MohamadAminGhanoum/Smart-room-Screen/assets/Screenshot 2026-01-31 at 23.26.51.png

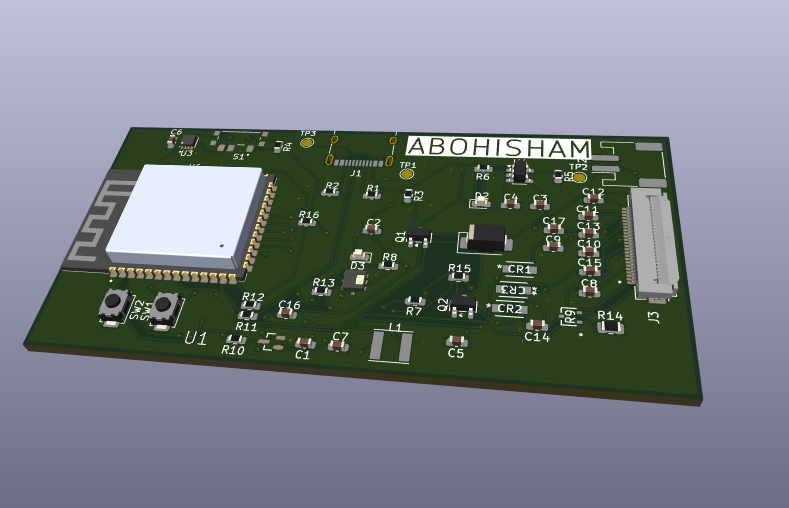
assets/Screenshot 2026-01-31 at 23.26.51.png
