MohamadAminGhanoum/Smart-room-Screen/assets/Screenshot 2026-01-23 at 23.30.38.png

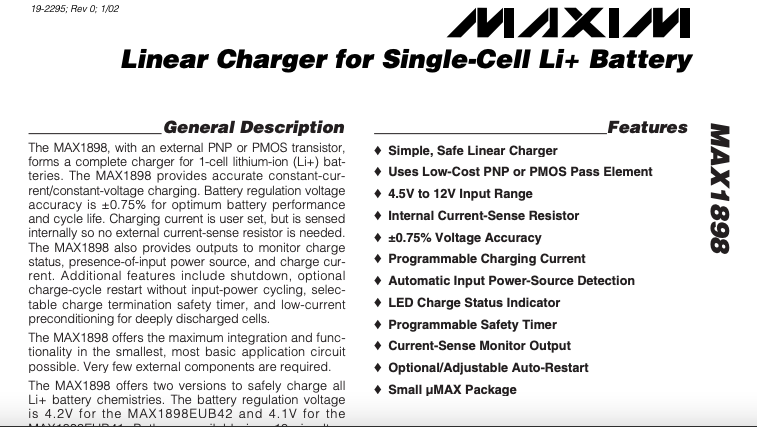
assets/Screenshot 2026-01-23 at 23.30.38.png
