MohamadAminGhanoum/Smart-room-Screen/assets/Screenshot 2026-01-24 at 14.30.04.png

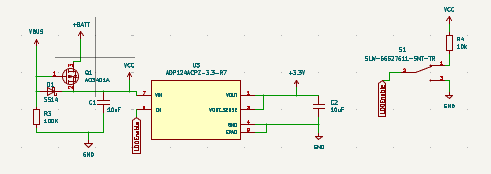
assets/Screenshot 2026-01-24 at 14.30.04.png
