MohamadAminGhanoum/Smart-room-Screen/assets/Screenshot 2026-01-24 at 15.07.33.png

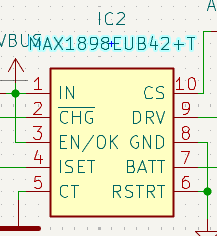
assets/Screenshot 2026-01-24 at 15.07.33.png
