MohamadAminGhanoum/Smart-room-Screen/assets/Screenshot 2026-01-24 at 16.34.39.png

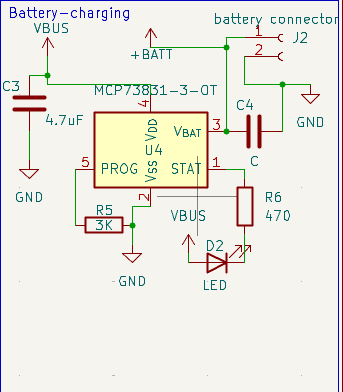
assets/Screenshot 2026-01-24 at 16.34.39.png
