MohamadAminGhanoum/Smart-room-Screen/assets/Screenshot 2026-01-24 at 16.39.06.png

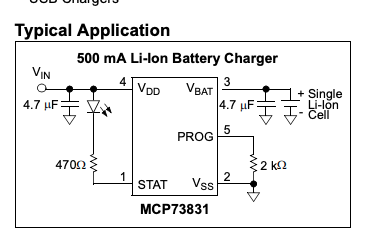
assets/Screenshot 2026-01-24 at 16.39.06.png
