MohamadAminGhanoum/Smart-room-Screen/assets/Screenshot 2026-01-24 at 17.12.46.png

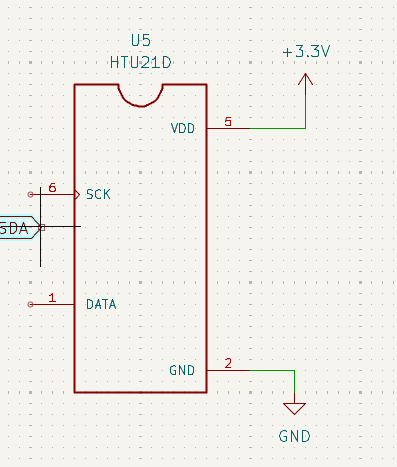
assets/Screenshot 2026-01-24 at 17.12.46.png
