MohamadAminGhanoum/Smart-room-Screen/assets/Screenshot 2026-01-24 at 17.20.51.png

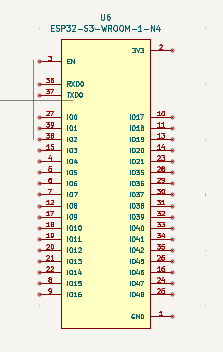
assets/Screenshot 2026-01-24 at 17.20.51.png
