MohamadAminGhanoum/Smart-room-Screen/assets/Screenshot 2026-01-24 at 19.51.00.png

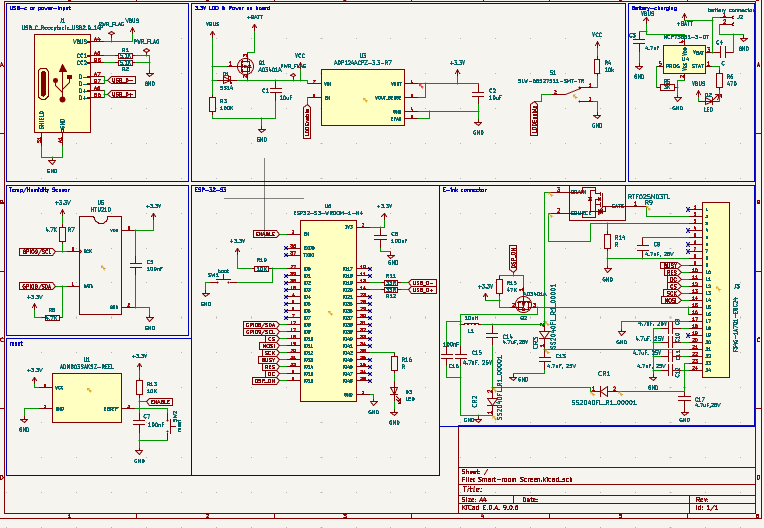
assets/Screenshot 2026-01-24 at 19.51.00.png
