MohamadAminGhanoum/Smart-room-Screen/assets/Screenshot 2026-01-24 at 19.59.05.png

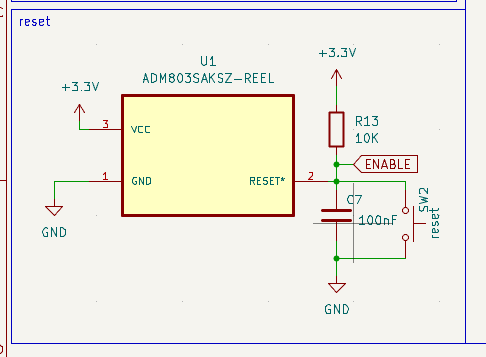
assets/Screenshot 2026-01-24 at 19.59.05.png
