MohamadAminGhanoum/Smart-room-Screen/assets/Screenshot 2026-01-24 at 20.54.59.png

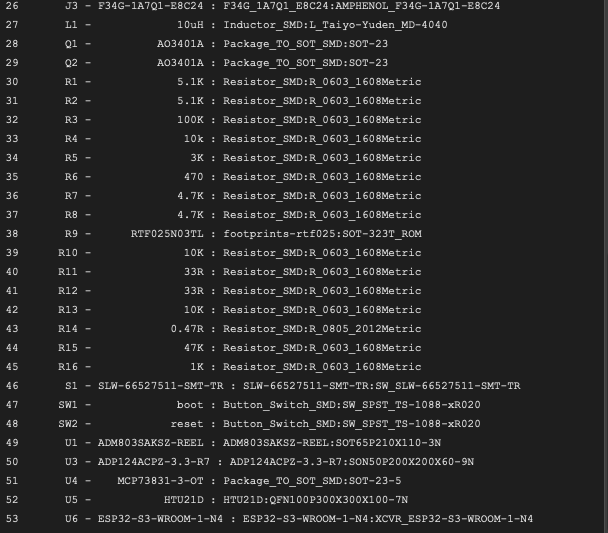
assets/Screenshot 2026-01-24 at 20.54.59.png
