MohamadAminGhanoum/Smart-room-Screen/assets/Screenshot 2026-01-25 at 15.22.35.png

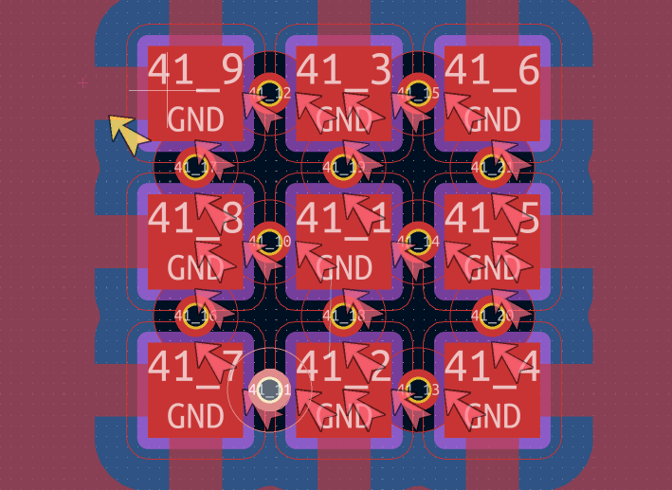
assets/Screenshot 2026-01-25 at 15.22.35.png
