MohamadAminGhanoum/Smart-room-Screen/assets/Screenshot 2026-02-18 at 13.43.28.png

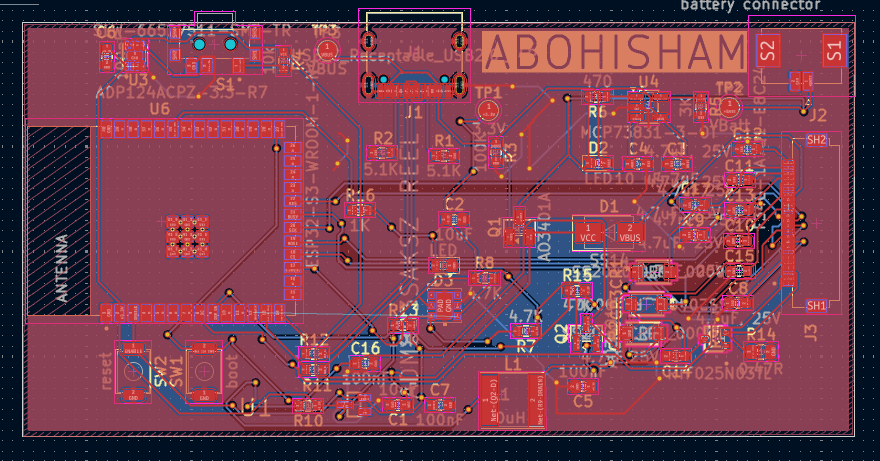
assets/Screenshot 2026-02-18 at 13.43.28.png
