MohamadAminGhanoum/Smart-room-Screen/assets/Screenshot 2026-02-18 at 15.10.17.png

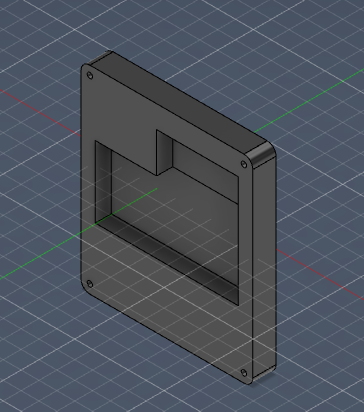
assets/Screenshot 2026-02-18 at 15.10.17.png
